samy/une-histoire-au-bout-du-fil/Boite_a_histoires/Ressources/Platine_cadran.png

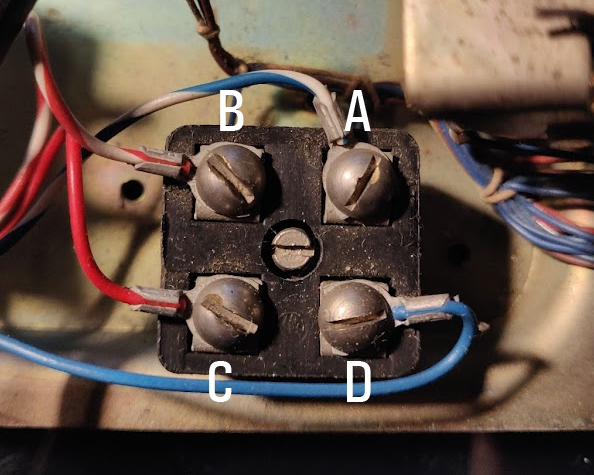
Boite_a_histoires/Ressources/Platine_cadran.png
