samy/une-histoire-au-bout-du-fil/Boite_a_histoires_S63/Breadboard_S63.png

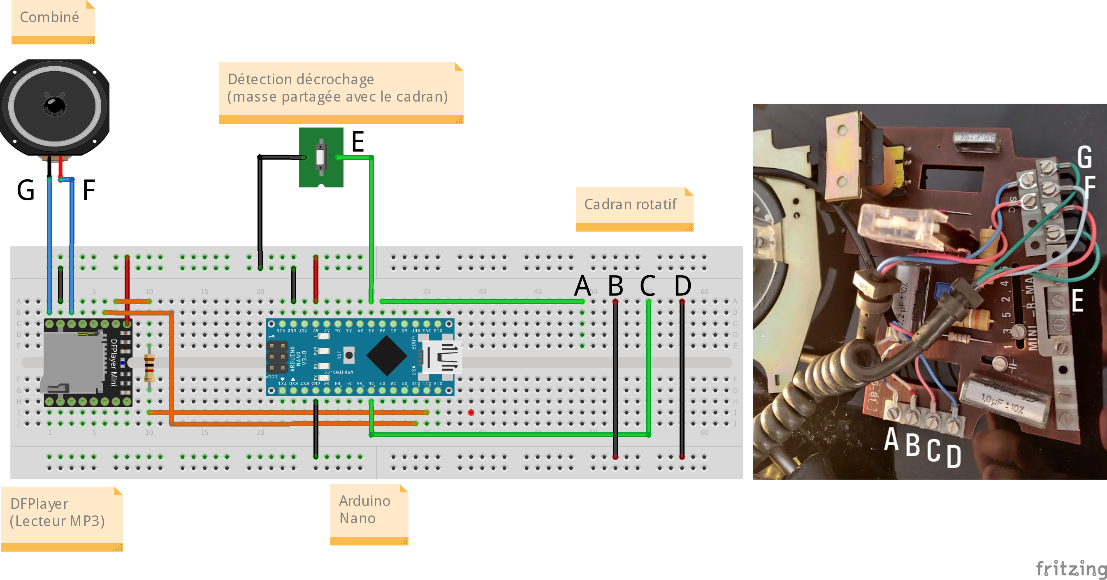
Boite_a_histoires_S63/Breadboard_S63.png
