samy/une-histoire-au-bout-du-fil/Boite_a_histoires_S63/Ressources/Platine.png

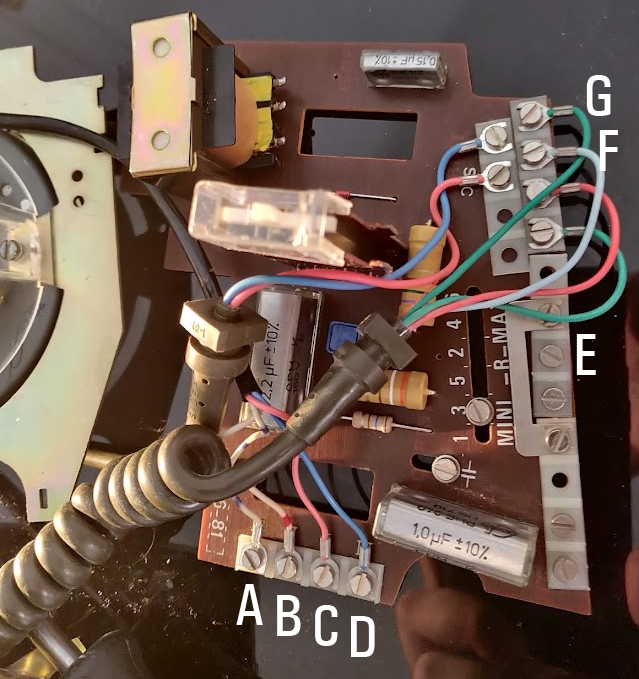
Boite_a_histoires_S63/Ressources/Platine.png
