samy/une-histoire-au-bout-du-fil/Boite_a_histoires_AOIP/src/OLED/Show_Lib.h

#ifndef __SHOW_LIB_H
#define __SHOW_LIB_H

//16 Gray Map
static const unsigned char gImage_ninja[8198] PROGMEM = { 0X00,0X04,0X80,0X00,0X80,0X00,
                                              0X00,0X00,0X00,0X00,0X00,0X00,0X00,0X00,0X00,0X00,0X00,0X00,0X00,0X00,0X00,0X00,
                                              0X00,0X00,0X00,0X00,0X00,0X00,0X00,0X00,0X00,0X00,0X00,0X00,0X00,0X00,0X00,0X00,
                                              0X00,0X00,0X00,0X00,0X00,0X00,0X00,0X00,0X00,0X00,0X00,0X00,0X00,0X00,0X00,0X00,
                                              0X00,0X00,0X00,0X00,0X00,0X00,0X00,0X00,0X00,0X00,0X00,0X00,0X00,0X00,0X00,0X00,
                                              0X00,0X00,0X00,0X00,0X00,0X00,0X00,0X00,0X00,0X00,0X00,0X00,0X00,0X00,0X00,0X00,
                                              0X00,0X00,0X00,0X00,0X00,0X00,0X00,0X00,0X00,0X00,0X00,0X00,0X00,0X00,0X00,0X00,
                                              0X00,0X00,0X00,0X00,0X00,0X00,0X00,0X00,0X00,0X00,0X00,0X00,0X00,0X00,0X00,0X00,
                                              0X00,0X00,0X00,0X00,0X00,0X00,0X00,0X00,0X00,0X00,0X00,0X00,0X00,0X00,0X00,0X00,
                                              0X00,0X00,0X00,0X00,0X00,0X00,0X00,0X00,0X00,0X00,0X00,0X00,0X00,0X00,0X00,0X00,
                                              0X00,0X00,0X00,0X00,0X00,0X00,0X00,0X00,0X00,0X00,0X00,0X00,0X00,0X00,0X00,0X00,
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
    0x18,0x54,0x32,0x1C,0x1C,0x32,0x54,0x18
};

static const uint8_t GPRS88[8] PROGMEM = { //GPRS
    0xC3,0x99,0x24,0x20,0x2C,0x24,0x99,0xC3
};

static const uint8_t Alarm88[8] PROGMEM = { //alram
    0xC3,0xBD,0x42,0x52,0x4E,0x42,0x3C,0xC3
};
//bit map end

#endif
